dslik/mix-effect/2810A/2810-0401/latest/pcb_top.png

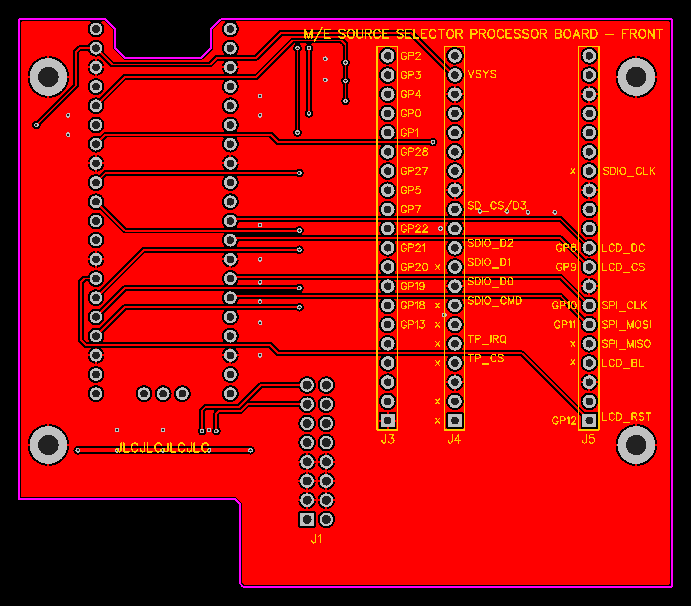
2810A/2810-0401/latest/pcb_top.png
