dslik/mix-effect/2810A/2810-8010/images/2810A.jpg

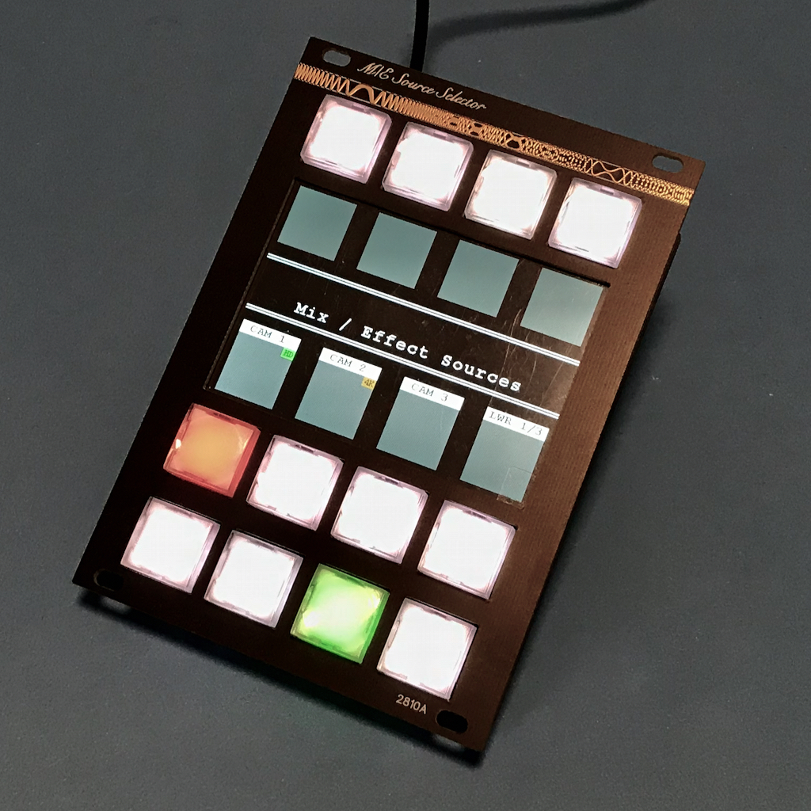
2810A/2810-8010/images/2810A.jpg
