dslik/mix-effect/2811A/2811-0101/latest/pcb_top.png

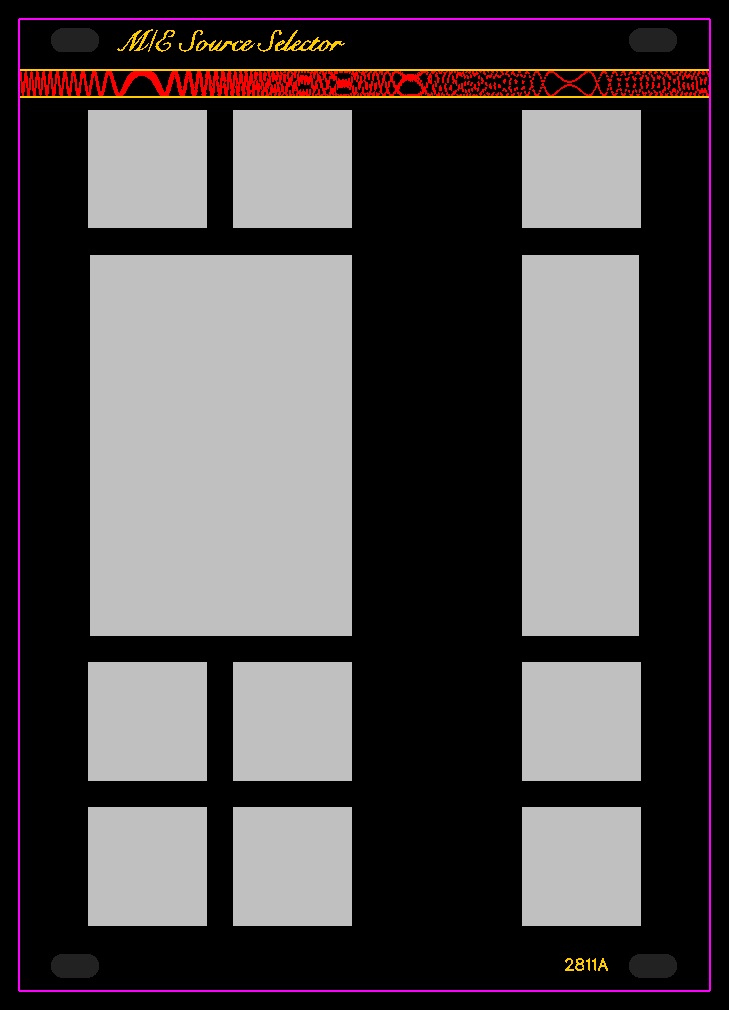
2811A/2811-0101/latest/pcb_top.png
