dslik/mix-effect/2820A/2820-0202/latest/pcb_bottom.png

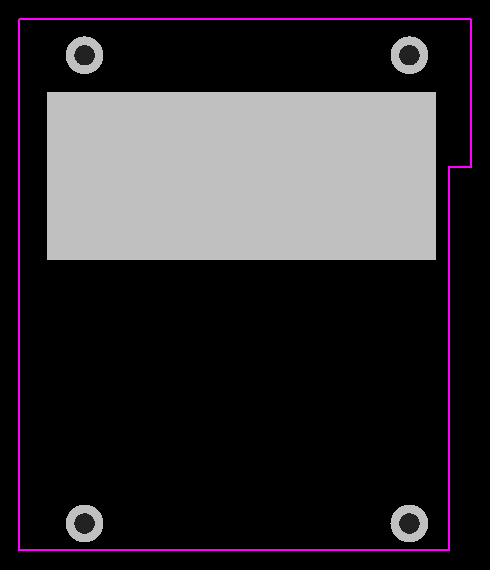
2820A/2820-0202/latest/pcb_bottom.png
