dslik/mix-effect/2820A/2820-0301/latest/pcb_top.png

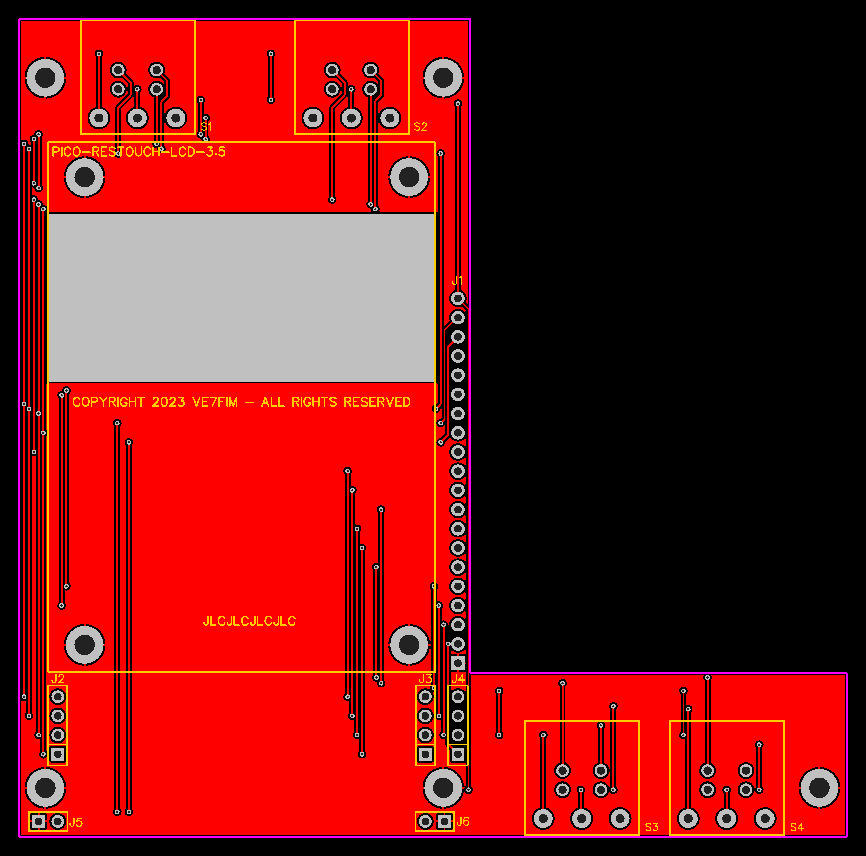
2820A/2820-0301/latest/pcb_top.png
