dslik/mix-effect/2820A/2820-0401/latest/pcb_bottom.png

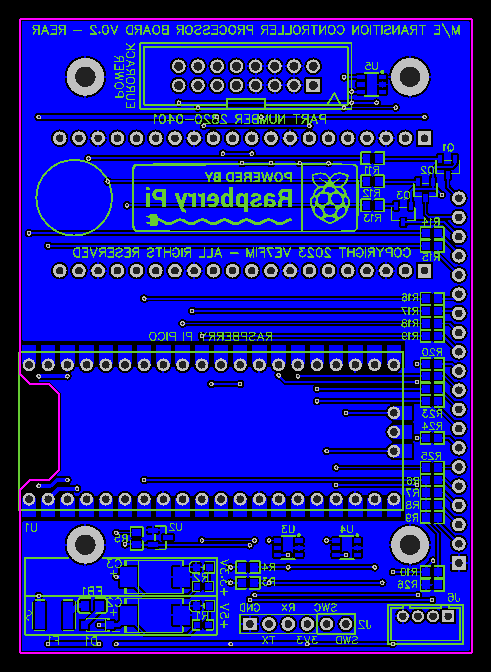
2820A/2820-0401/latest/pcb_bottom.png
