dslik/mix-effect/2821A/2821-0101/latest/pcb_bottom.png

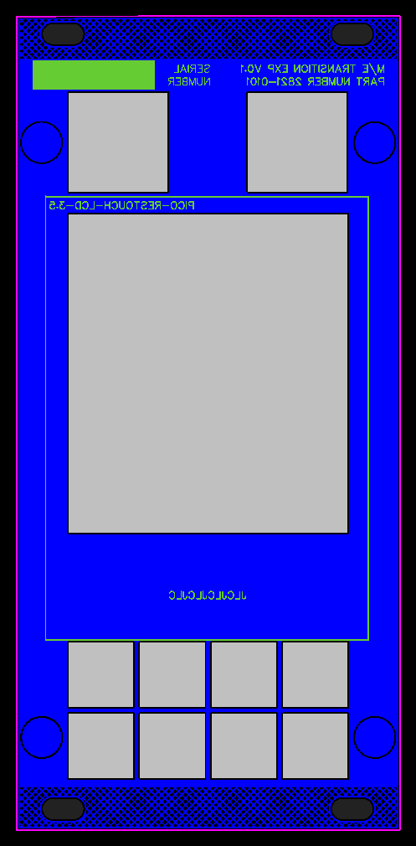
2821A/2821-0101/latest/pcb_bottom.png
