dslik/mix-effect/2821A/2821-0111/latest/pcb_top.png

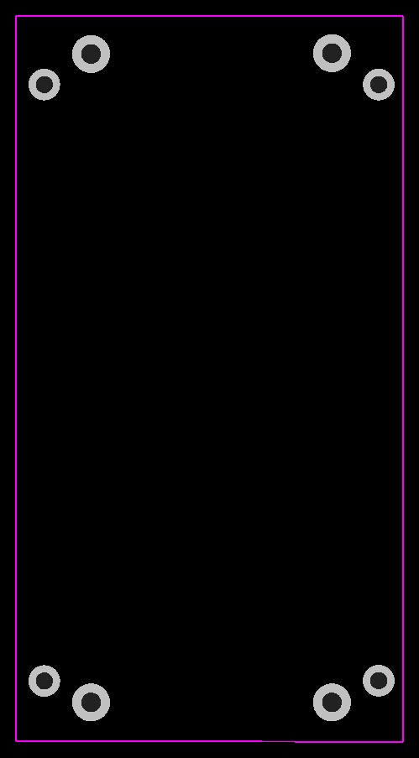
2821A/2821-0111/latest/pcb_top.png
