dslik/mix-effect/2821A/2821-0201/latest/pcb_top.png

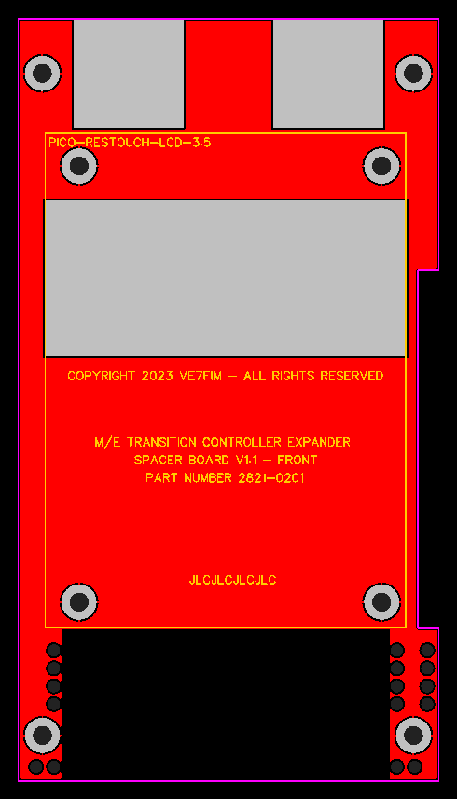
2821A/2821-0201/latest/pcb_top.png
