dslik/mix-effect/2821A/2821-0301/latest/pcb_top.png

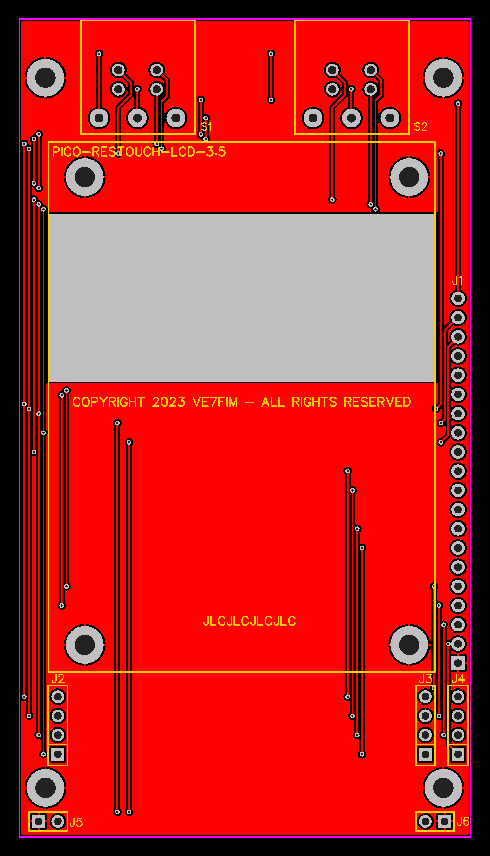
2821A/2821-0301/latest/pcb_top.png
