dslik/mix-effect/2850A/2850-0201/latest/pcb_bottom.png

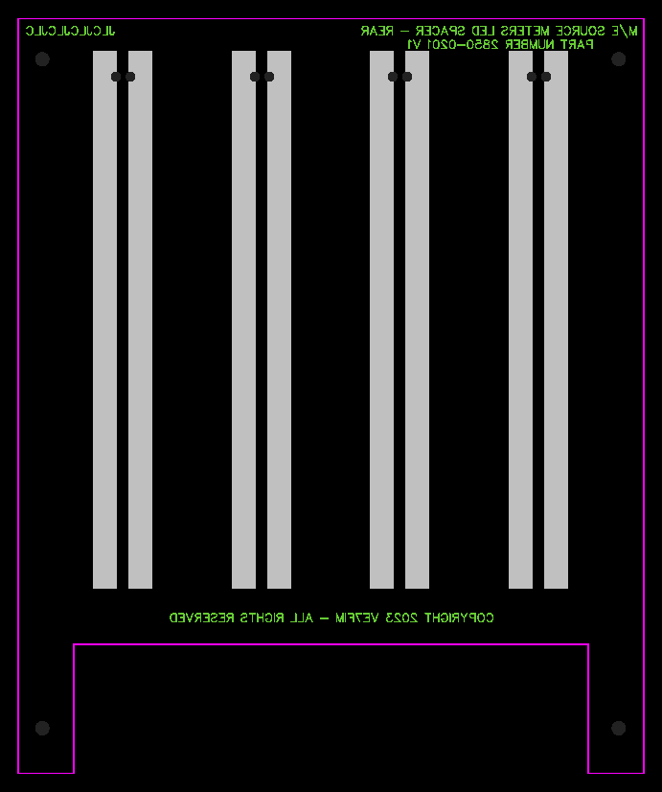
2850A/2850-0201/latest/pcb_bottom.png
