dslik/mix-effect/2850A/2850-0301/latest/pcb_top.png

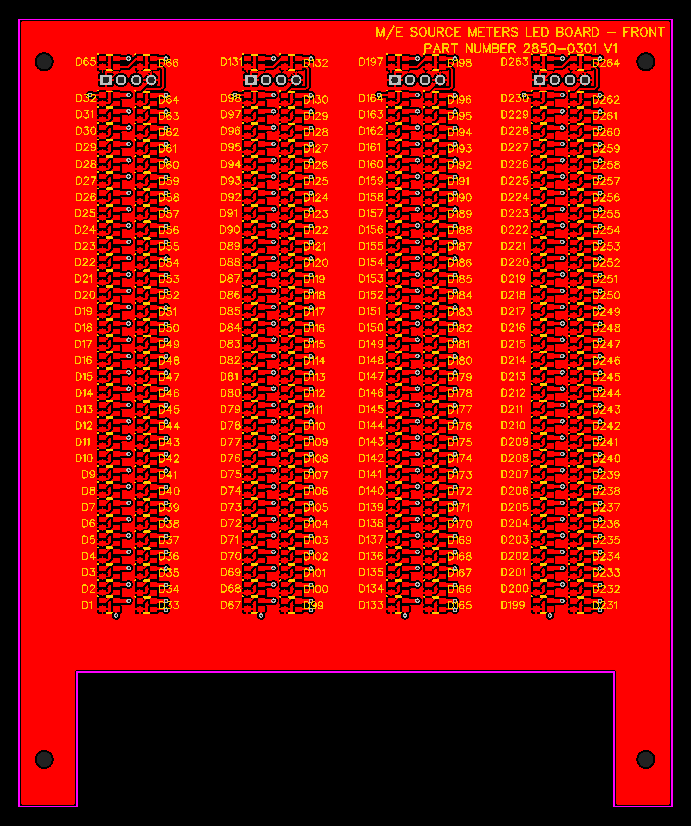
2850A/2850-0301/latest/pcb_top.png
