dslik/mix-effect/2850A/2850-0401/latest/pcb_top.png

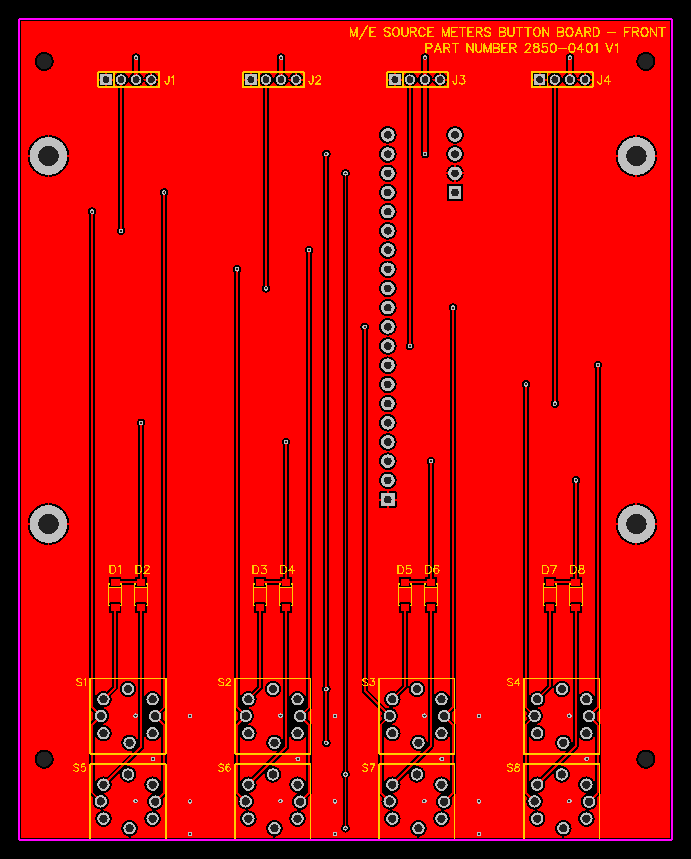
2850A/2850-0401/latest/pcb_top.png
