dslik/mix-effect/2851A/2851-0301/latest/pcb_bottom.png

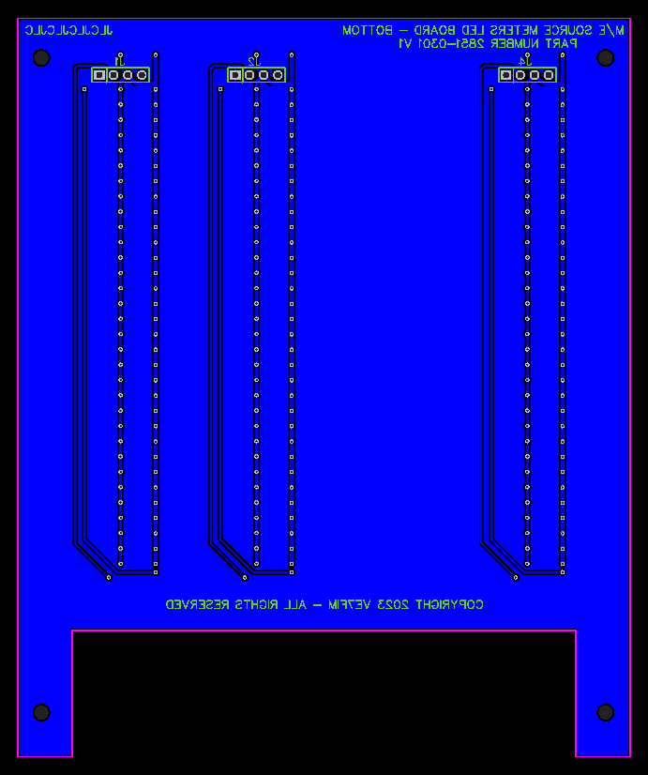
2851A/2851-0301/latest/pcb_bottom.png
