dslik/mix-effect/2851A/2851-0401/latest/pcb_top.png

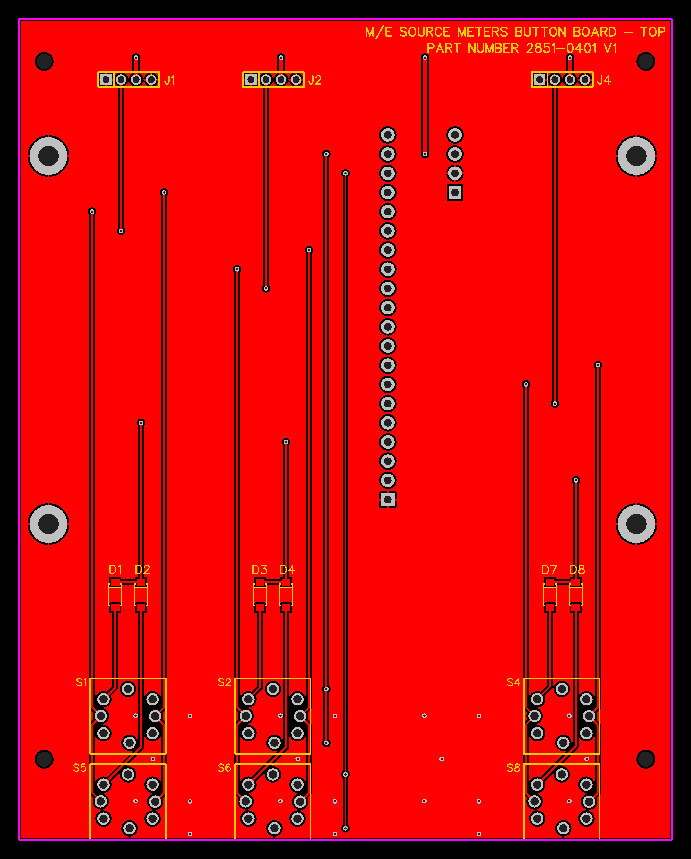
2851A/2851-0401/latest/pcb_top.png
