dslik/mix-effect/2860A/2860-0101/latest/pcb_top.png

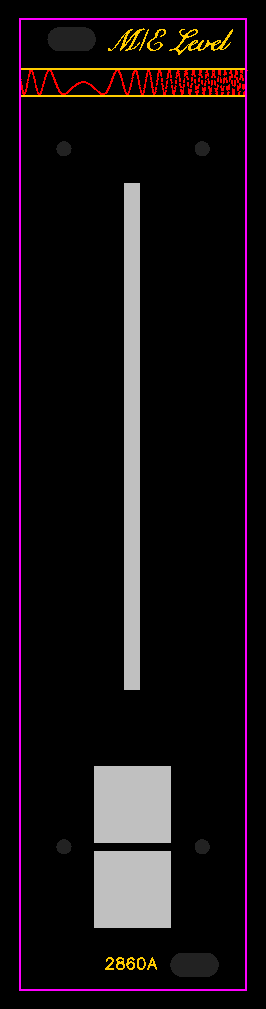
2860A/2860-0101/latest/pcb_top.png
