dslik/mix-effect/2860A/2860-0201/latest/pcb_bottom.png

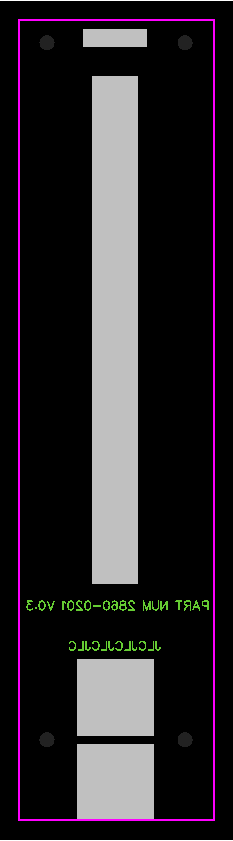
2860A/2860-0201/latest/pcb_bottom.png
