dslik/mix-effect/2860A/2860-0301/latest/pcb_bottom.png

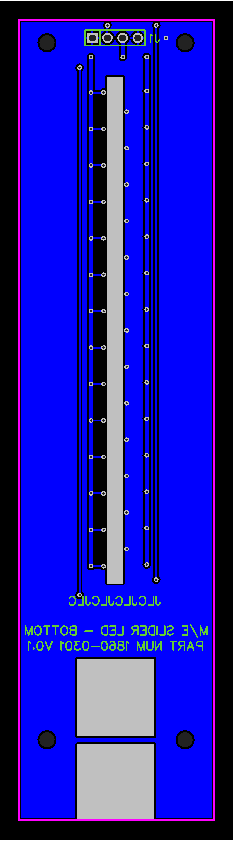
2860A/2860-0301/latest/pcb_bottom.png
