dslik/mix-effect/2880A/2880-0201/latest/pcb_bottom.png

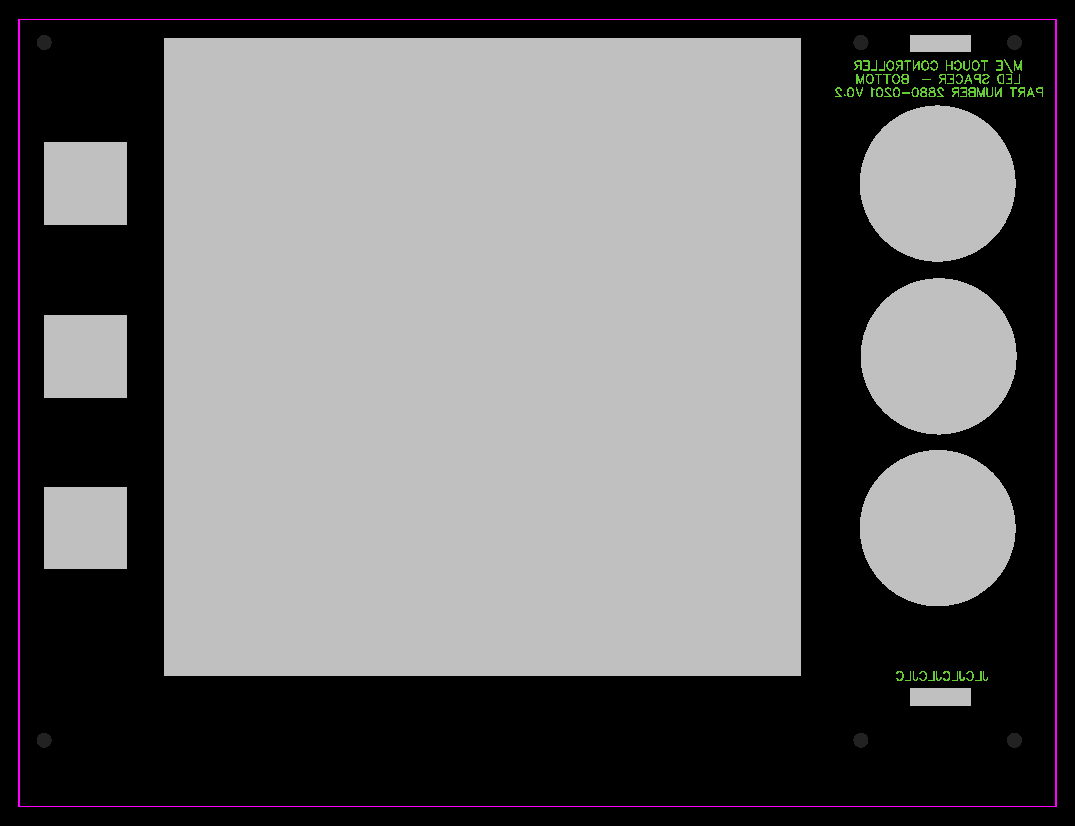
2880A/2880-0201/latest/pcb_bottom.png
