dslik/mix-effect/2880A/2880-0301/latest/pcb_bottom.png

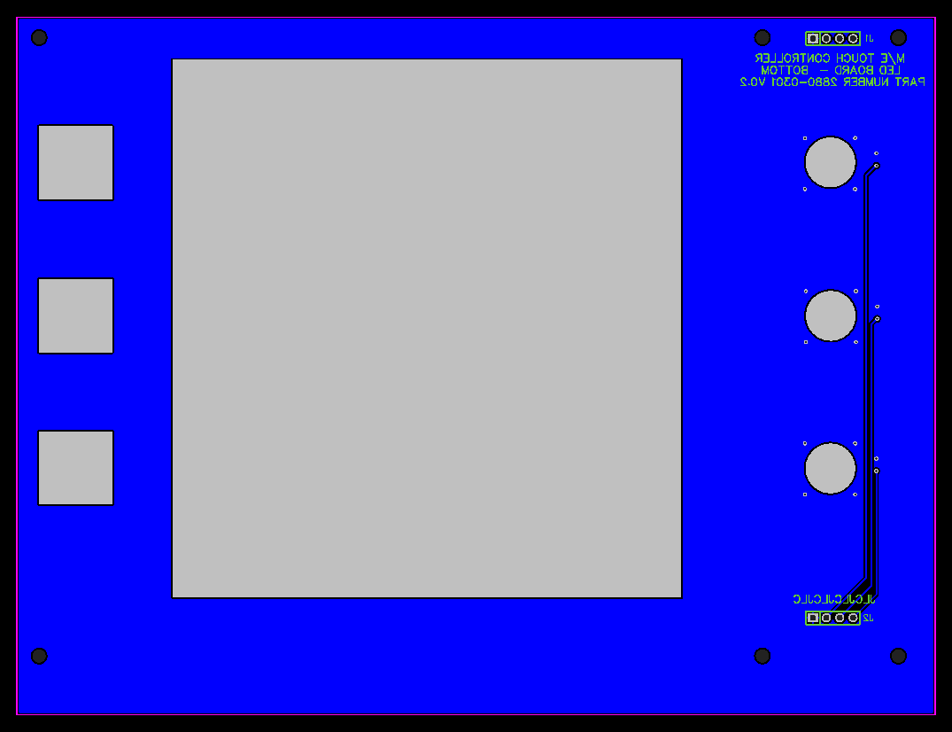
2880A/2880-0301/latest/pcb_bottom.png
