dslik/mix-effect/2880A/2880-0401/latest/pcb_bottom.png

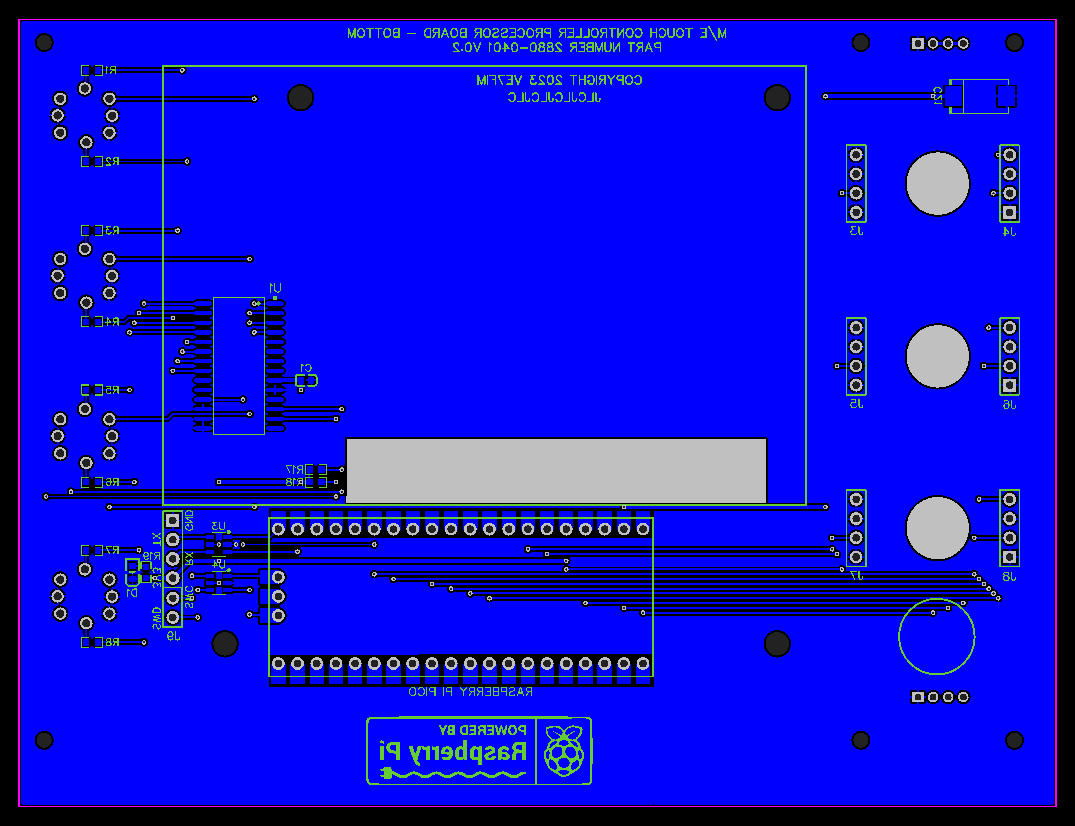
2880A/2880-0401/latest/pcb_bottom.png
