dslik/mix-effect/2880A/2880-0401/latest/pcb_top.png

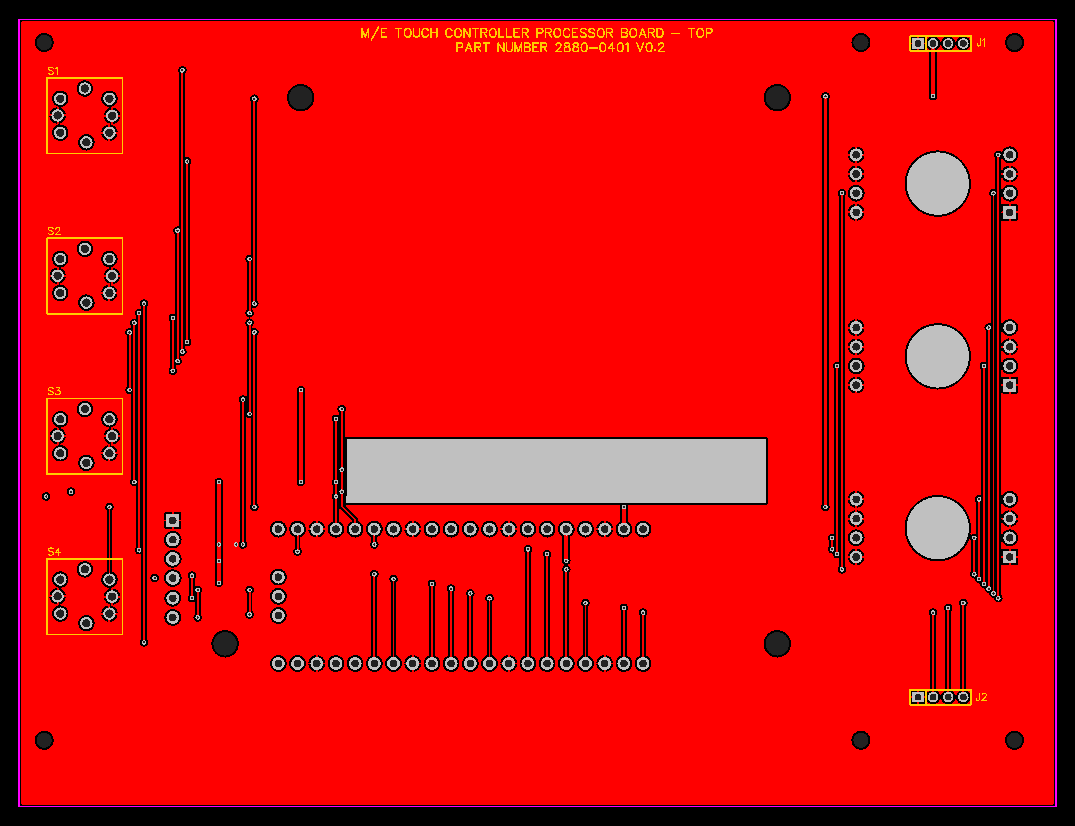
2880A/2880-0401/latest/pcb_top.png
