dslik/mix-effect/2890A/2890-0201/latest/pcb_bottom.png

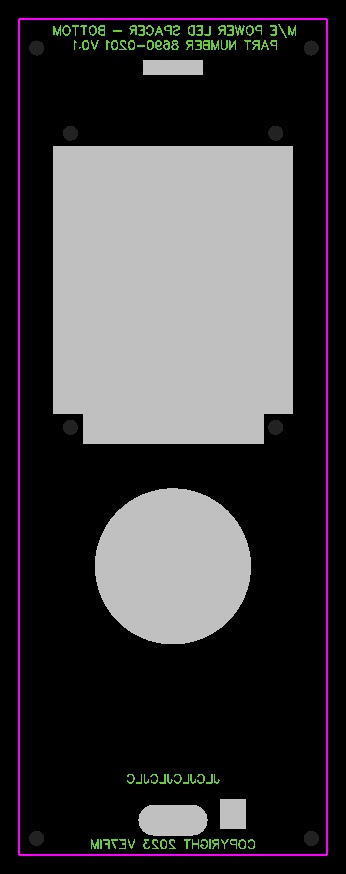
2890A/2890-0201/latest/pcb_bottom.png
