dslik/mix-effect/2890A/2890-0301/latest/pcb_bottom.png

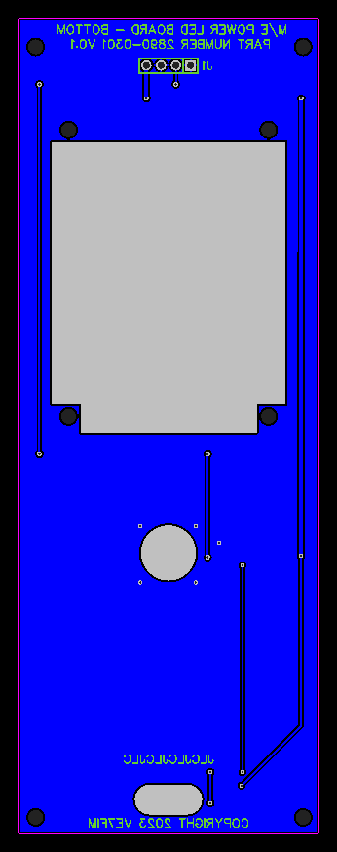
2890A/2890-0301/latest/pcb_bottom.png
