dslik/mix-effect/2890A/2890-0501/latest/pcb_top.png

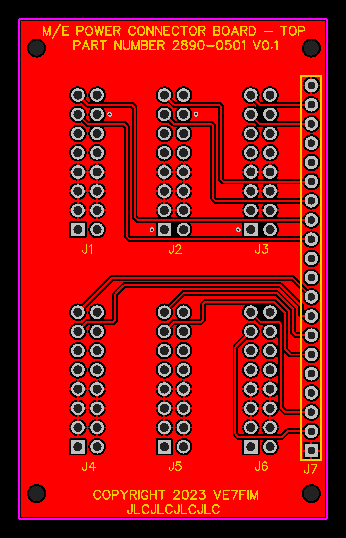
2890A/2890-0501/latest/pcb_top.png
