dslik/mix-effect/2850A/2850-0401/latest/bom.csv

ID | Name | Designator | Footprint | Quantity | Manufacturer Part | Manufacturer | Supplier | Supplier Part | Price
1 | B3W-9_2-LED | S1,S2,S3,S4,S5,S6,S7,S8 | B3W-9_2-LED | 8
2 | SOD-123_L2.8-W1.8-LS3.7-RD | D2,D3,D1,D4,D6,D5,D8,D7 | SOD-123_L2.8-W1.8-LS3.7-RD | 8 | 1N4148W-7-F | DIODES | LCSC | C83528 | 0.01
3 | HDR-TH_4P-P2.00-V-M | J2,J3,J4,J1 | HDR-TH_4P-P2.00-V-M | 4 | DZ200R-11-04-39 | DEALON(德艺隆) | LCSC | C2935903 | 0.019
4 | HDR-TH_4P-P2.54-V | J5 | HDR-TH_4P-P2.54-V | 1 | 210S-1*4P L=11.6MMGold-plated black | Ckmtw | LCSC | C124378 | 0.042
5 | HDR-TH_20P-P2.54-V-F | J6 | HDR-TH_20P-P2.54-V-F | 1
