dslik/mix-effect/2820A/2820-0301/latest/bom.csv

ID | Name | Designator | Footprint | Quantity | Manufacturer Part | Manufacturer | Supplier | Supplier Part | Price
1 | HDR-TH_2P-P2.54-V-M | J5,J6 | HDR-TH_2P-P2.54-V-M | 2 | PZ254V-11-02P | XFCN(兴飞) | LCSC | C492401 | 0.014
2 | SOD-123_L2.8-W1.8-LS3.7-RD | C4,D3,D1,D2 | SOD-123_L2.8-W1.8-LS3.7-RD | 4 | 1N4148W-7-F | DIODES | LCSC | C83528 | 0.01
3 | HDR-TH_20P-P2.54-V-F | J1 | HDR-TH_20P-P2.54-V-F | 1
4 | HDR-TH_4P-P2.54-V-M | J2,J3,J4 | HDR-TH_4P-P2.54-V-M | 3
