dslik/mix-effect/2820A/2820-0302/latest/bom.csv

ID | Name | Designator | Footprint | Quantity | Manufacturer Part | Manufacturer | Supplier | Supplier Part | Price
1 | SOD-123_L2.8-W1.8-LS3.7-RD | D1,D2,D3,D4,D5,D6,D7,D8 | SOD-123_L2.8-W1.8-LS3.7-RD | 8 | 1N4148W-7-F | DIODES | LCSC | C83528 | 0.01
2 | HDR-TH_2P-P2.54-V-M | J5,J6 | HDR-TH_2P-P2.54-V-M | 2 | PZ254V-11-02P | XFCN(兴飞) | LCSC | C492401 | 0.014
3 | HDR-TH_4P-P2.54-V-M | J2,J3,J4 | HDR-TH_4P-P2.54-V-M | 3
4 | B3W-9_2-LED | S12,S11,S10,S9,S5,S6,S7,S8 | B3W-9_2-LED | 8
