dslik/mix-effect/2810A/2810-0301/latest/bom.csv

ID | Name | Designator | Footprint | Quantity | Manufacturer Part | Manufacturer | Supplier | Supplier Part | Price
1 | SOD-123_L2.8-W1.8-LS3.7-RD | D9,D12,D8,D11,D10,D7,D1,D2,D3,D4,D5,D6 | SOD-123_L2.8-W1.8-LS3.7-RD | 12 | 1N4148W-7-F | DIODES | LCSC | C83528 | 0.01
2 | HDR-TH_20P-P2.54-V-F | CN3 | HDR-TH_20P-P2.54-V-F | 1
