dslik/mix-effect/2851A/2851-0301/latest/bom.csv

ID | Name | Designator | Footprint | Quantity | Manufacturer Part | Manufacturer | Supplier | Supplier Part | Price
1 | LED-SMD_4P-L2.0-W2.0-TL_WS2812B-2020 | D67,D80,D79,D78,D77,D76,D75,D74,D73,D72,D71,D70,D69,D68,D81,D82,D83,D84,D85,D86,D87,D88,D89,D90,D91,D92,D93,D94,D95,D96,D97,D98,D99,D100,D101,D102,D103,D104,D105,D106,D107,D108,D109,D110,D111,D112,D113,D114,D115,D116,D117,D118,D119,D120,D121,D122,D123,D124,D125,D126,D127,D128,D129,D130,D131,D132,D199,D212,D211,D210,D209,D208,D207,D206,D205,D204,D203,D202,D201,D200,D213,D214,D215,D216,D217,D218,D219,D220,D221,D222,D223,D224,D225,D226,D227,D228,D229,D230,D231,D232,D233,D234,D235,D236,D237,D238,D239,D240,D241,D242,D243,D244,D245,D246,D247,D248,D249,D250,D251,D252,D253,D254,D255,D256,D257,D258,D259,D260,D261,D262,D263,D264,D1,D14,D13,D12,D11,D10,D9,D8,D7,D6,D5,D4,D3,D2,D15,D16,D17,D18,D19,D20,D21,D22,D23,D24,D25,D26,D27,D28,D29,D30,D31,D32,D33,D34,D35,D36,D37,D38,D39,D40,D41,D42,D43,D44,D45,D46,D47,D48,D49,D50,D51,D52,D53,D54,D55,D56,D57,D58,D59,D60,D61,D62,D63,D64,D65,D66 | LED-SMD_4P-L2.0-W2.0-TL_WS2812B-2020 | 198 | WS2812C-2020-V1 | worldsemi | LCSC | C2976072 | 0.099
2 | HDR-TH_4P-P2.00-V-M | J2,J4,J1 | HDR-TH_4P-P2.00-V-M | 3 | DZ200R-11-04-39 | DEALON(德艺隆) | LCSC | C2935903 | 0.019
