dslik/mix-effect/2810A/2810-0401/latest/bom.csv

ID | Name | Designator | Footprint | Quantity | Manufacturer Part | Manufacturer | Supplier | Supplier Part | Price
1 | R0603 | R10 | R0603 | 1 | 0603WAF3901T5E | UNI-ROYAL(厚声) | LCSC | C23018 | 0.001
2 | R0603 | R9 | R0603 | 1 | 0603WAF3001T5E | UNI-ROYAL(厚声) | LCSC | C4211 | 0.001
3 | CONN-SMD_SM03B-SRSS-TB-LF-SN-P | J2,J6 | CONN-SMD_SM03B-SRSS-TB-LF-SN-P | 2 | SM03B-SRSS-TB(LF)(SN) | JST | LCSC | C160403 | 0.137
4 | LED0603-R-RD | D2,D1 | LED0603-R-RD | 2 | 19-217/GHC-YR1S2/3T | EVERLIGHT(亿光) | LCSC | C72043 | 0.027
5 | F1812 | F1 | F1812 | 1 | MINISMDC020F-2 | Littelfuse(美国力特) | LCSC | C5418 | 0.165
6 | SOT-23-6_L2.9-W1.6-P0.95-LS2.8-BL | U4,U5,U3 | SOT-23-6_L2.9-W1.6-P0.95-LS2.8-BL | 3 | USBLC6-2SC6 | ST(意法半导体) | LCSC | C7519 | 0.118
7 | R0603 | R14,R15,R16,R17,R18,R19,R20,R21,R22,R23,R24,R25 | R0603 | 12 | 0603WAF3300T5E | UNI-ROYAL(厚声) | LCSC | C23138 | 0.001
8 | SOT-23-3_L3.0-W1.7-P0.95-LS2.9-BR | Q1,Q2,Q3 | SOT-23-3_L3.0-W1.7-P0.95-LS2.9-BR | 3 | MMBT3906LT1 | LGE(鲁光) | LCSC | C402273 | 0.013
9 | CAP-SMD_L7.3-W4.3-R-RD | C2,C1 | CAP-SMD_L7.3-W4.3-R-RD | 2 | TPSD226K025R0200 | Kyocera AVX | LCSC | C284839 | 0.546
10 | R0603 | R11,R12,R13,R7,R6,R8 | R0603 | 6 | 0603WAF1002T5E | UNI-ROYAL(厚声) | LCSC | C25804 | 0.001
11 | SOT-23-3_L2.9-W1.6-P1.90-LS2.8-BR | U2 | SOT-23-3_L2.9-W1.6-P1.90-LS2.8-BR | 1 | LM4040CIM3-3.0/NOPB | TI(德州仪器) | LCSC | C132056 | 0.905
12 | R0603 | R26 | R0603 | 1 | 0603WAF1001T5E | UNI-ROYAL(厚声) | LCSC | C21190 | 0.001
13 | R0603 | R2,R1,R5,R4,R3 | R0603 | 5 | 0603WAF2002T5E | UNI-ROYAL(厚声) | LCSC | C4184 | 0.001
14 | SOD-123_L2.8-W1.8-LS3.7-RD | D3 | SOD-123_L2.8-W1.8-LS3.7-RD | 1 | 1N4148W-7-F | DIODES | LCSC | C83528 | 0.01
15 | L0805 | FB1 | L0805 | 1 | GZ2012D601TF | Sunlord | LCSC | C1017 | 0.01
