dslik/mix-effect/2810A/2810-8010/images/pcb_2810-0401_front.pdf

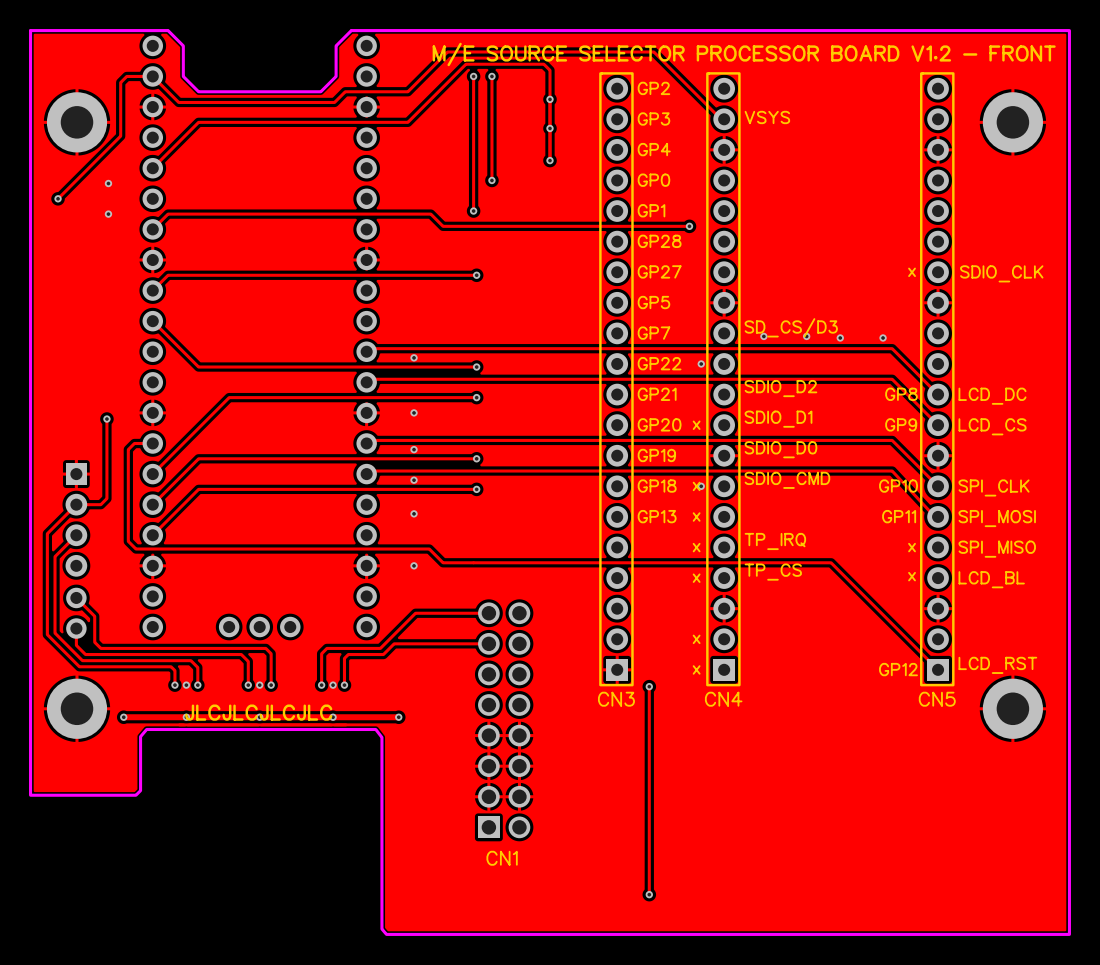
[picture p168: page 1]
