dslik/mix-effect/2810A/2810-8010/images/pcb_2810-0401_rear.pdf

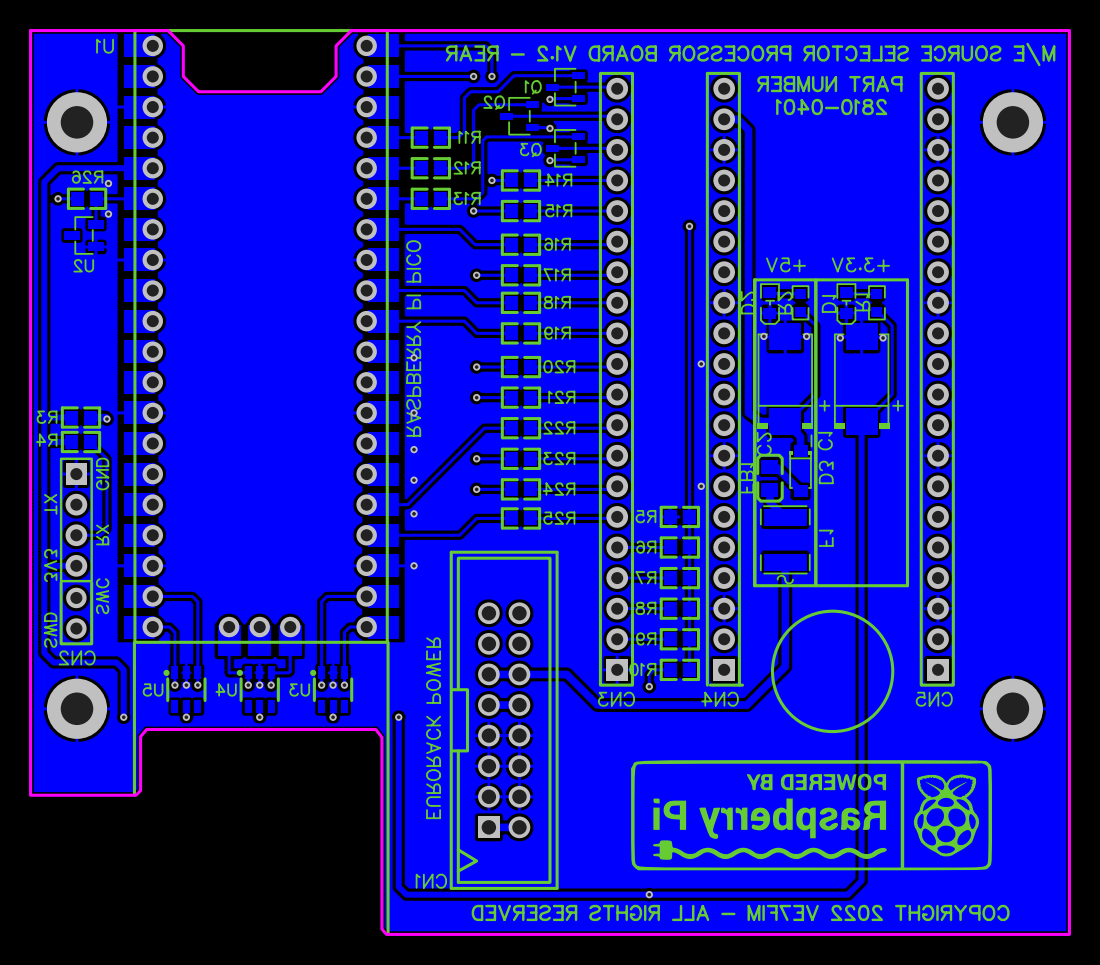
[picture p169: page 1]
